barrettotte/cat-feeder/fusion360/servo-cover.3mf

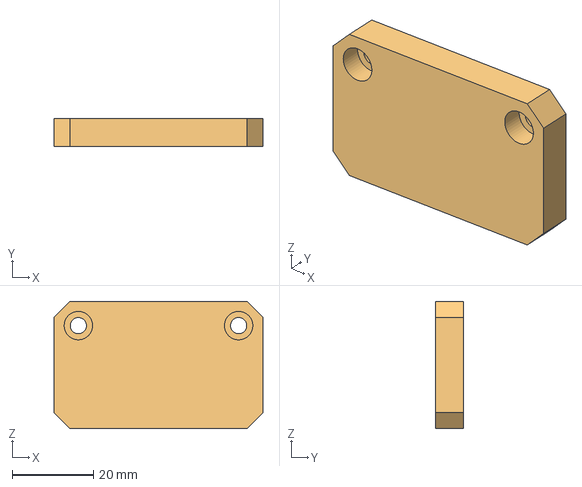
[picture p21: CAD file, 2022-12-23]
fusion360/servo-cover.3mf
51.5 x 7.00 x 31.4 mm
