barrettotte/cat-feeder/fusion360/hopper.3mf

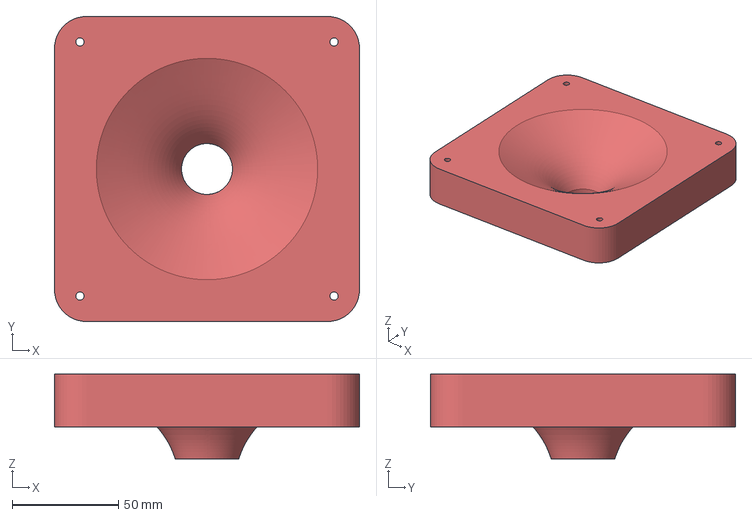
[picture p22: CAD file, 2022-12-23]
fusion360/hopper.3mf
143.8 x 143.8 x 40.0 mm
