barrettotte/cat-feeder/fusion360/hopper-adapter.3mf

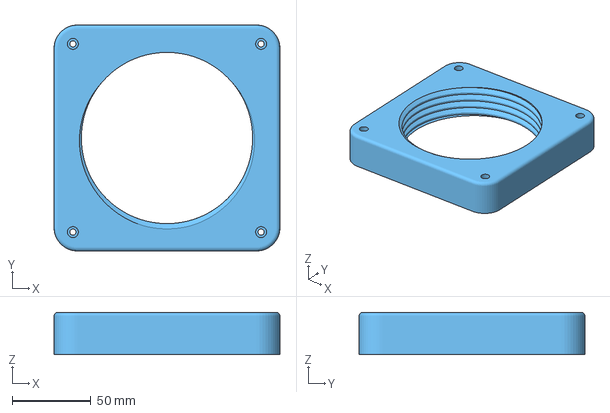
[picture p23: CAD file, 2022-12-23]
fusion360/hopper-adapter.3mf
143.8 x 143.8 x 27.0 mm
