barrettotte/cat-feeder/fusion360/enclosure-motor-foot.3mf

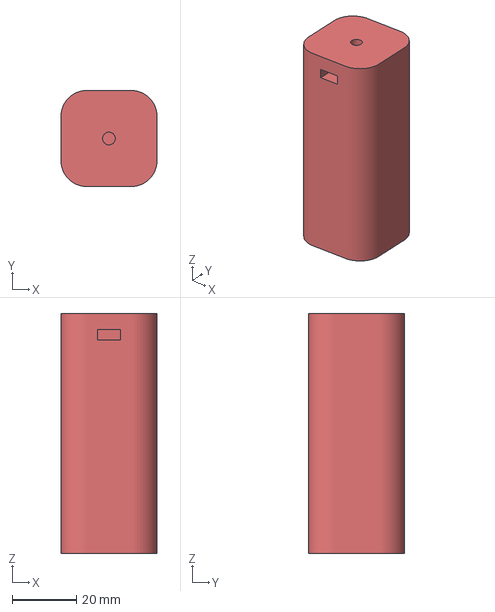
[picture p24: CAD file, 2022-12-23]
fusion360/enclosure-motor-foot.3mf
30.0 x 30.0 x 75.0 mm
