barrettotte/cat-feeder/fusion360/leg.3mf

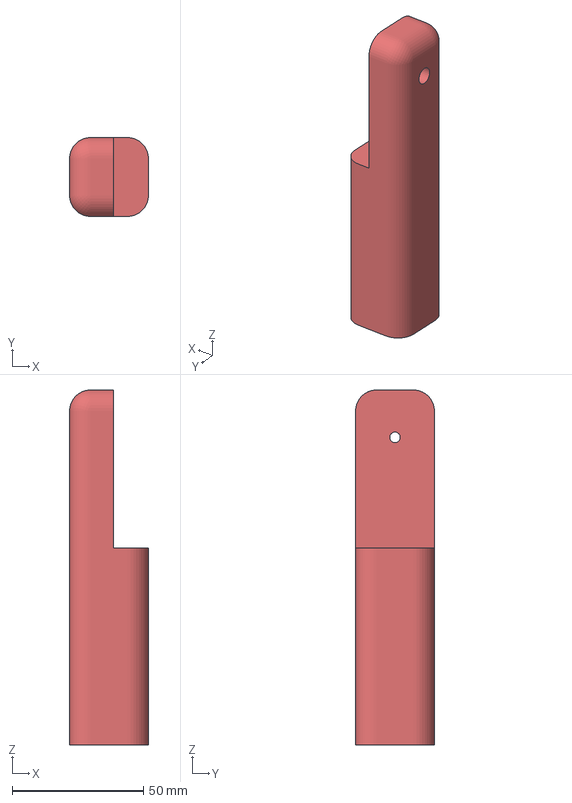
[picture p25: CAD file, 2022-12-23]
fusion360/leg.3mf
30.0 x 30.0 x 135.0 mm
