barrettotte/cat-feeder/kicad/cat-feeder.kicad_sch

## KiCad design kicad/cat-feeder.kicad_sch (2022-12-25, an earlier design)

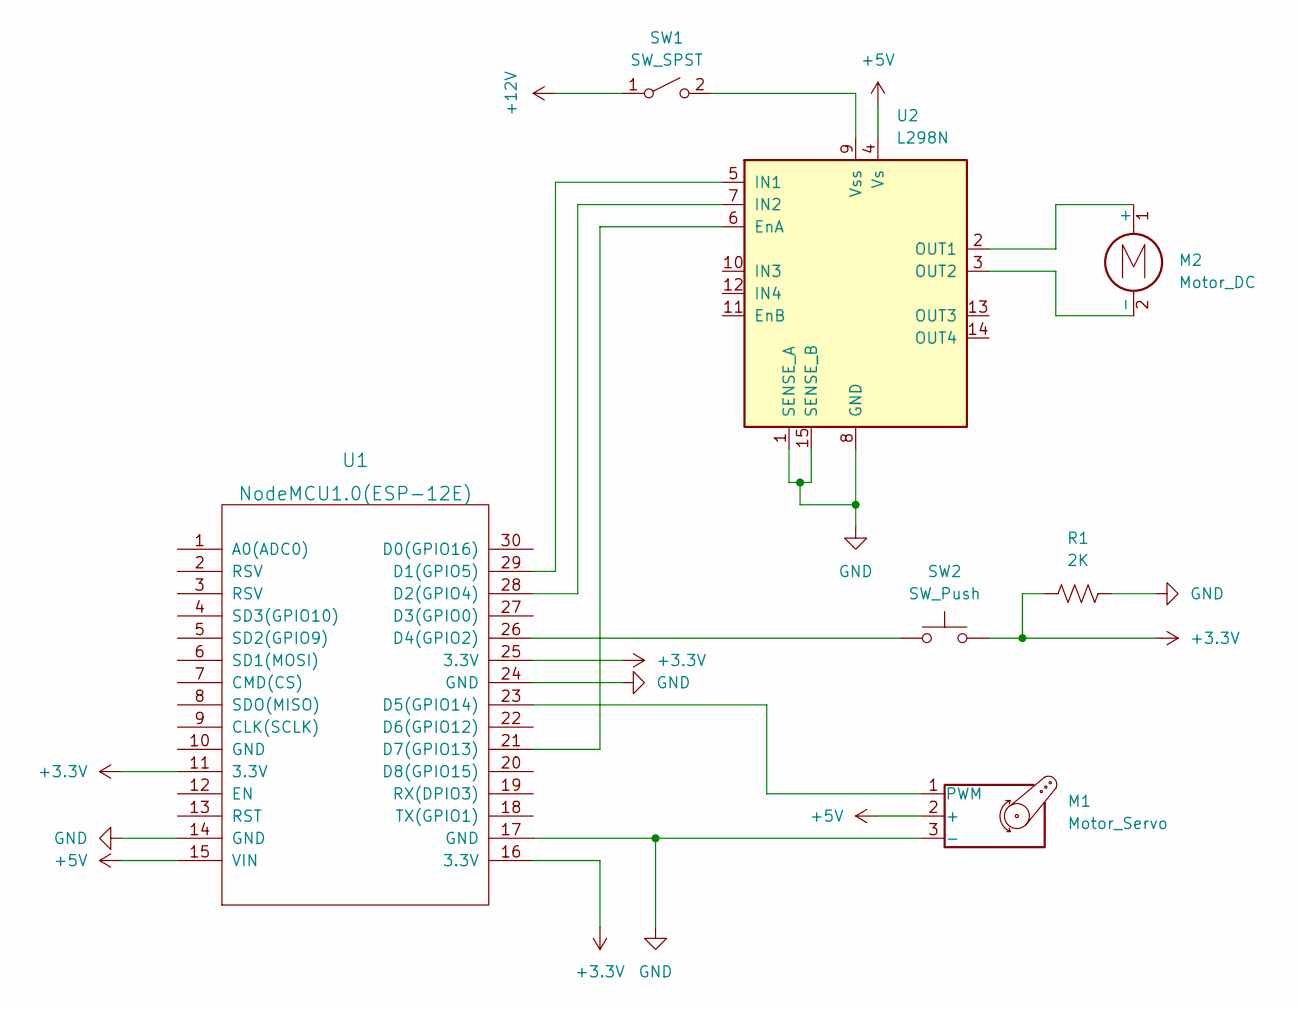
[picture p26: schematic cat-feeder.kicad_sch]

Parts:
M1: Motor_Servo
M2: Motor_DC
R1: 2K
SW1: SW_SPST
SW2: SW_Push
U1: NodeMCU1.0(ESP-12E)
U2: L298N; TO-220-15_P2.54x2.54mm_StaggerOdd_Lead4.58mm_Vertical

Connections:
+3.3V: R1.1, SW2.2, U1.11 (3.3V), U1.16 (3.3V), U1.25 (3.3V)
+5V: M1.2 (+), U1.15 (VIN), U2.4 (Vs)
+12V: SW1.1 (A)
GND: M1.3 (-), R1.2, U1.14 (GND), U1.17 (GND), U1.24 (GND), U2.1 (SENSE_A), U2.8 (GND), U2.15 (SENSE_B)
unnamed: M1.1 (PWM), U1.23 (D5(GPIO14))
unnamed: M2.1 (+), U2.2 (OUT1)
unnamed: M2.2 (-), U2.3 (OUT2)
unnamed: SW1.2 (B), U2.9 (Vss)
unnamed: SW2.1, U1.26 (D4(GPIO2))
unnamed: U1.21 (D7(GPIO13)), U2.6 (EnA)
unnamed: U1.28 (D2(GPIO4)), U2.7 (IN2)
unnamed: U1.29 (D1(GPIO5)), U2.5 (IN1)
